JordanAceto/it_is_the_champion/faceplate/docs/2D/it_is_the_champion_faceplate-bottom.jpg

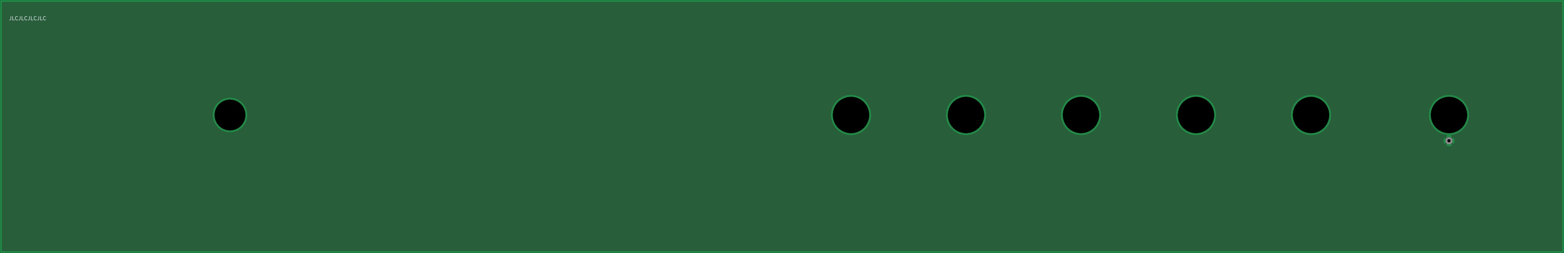
faceplate/docs/2D/it_is_the_champion_faceplate-bottom.jpg
