JordanAceto/it_is_the_champion/faceplate/docs/html_nav/images/cat_pdf_layers_it_is_the_champion_faceplate-B_Cu.png

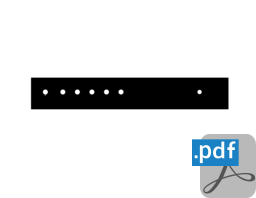
faceplate/docs/html_nav/images/cat_pdf_layers_it_is_the_champion_faceplate-B_Cu.png
