JordanAceto/it_is_the_champion/pcb/docs/2D/it_is_the_champion-bottom.jpg

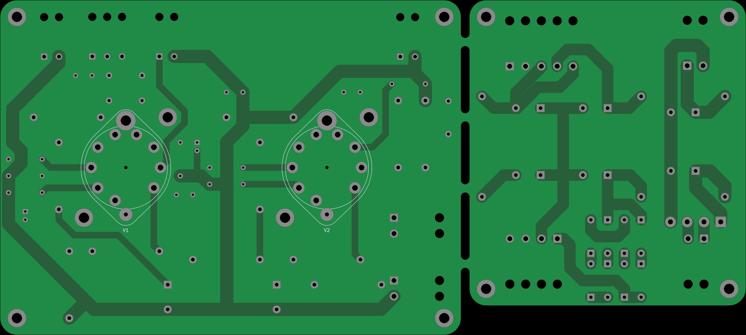
pcb/docs/2D/it_is_the_champion-bottom.jpg
