JordanAceto/it_is_the_champion/pcb/docs/html_nav/images/cat_pdf_layers_it_is_the_champion-B_Cu.png

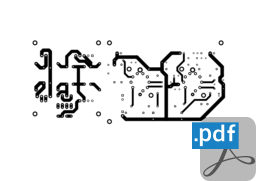
pcb/docs/html_nav/images/cat_pdf_layers_it_is_the_champion-B_Cu.png
