JordanAceto/it_is_the_champion/rear_panel/docs/2D/it_is_the_champion_rear_panel-bottom.jpg

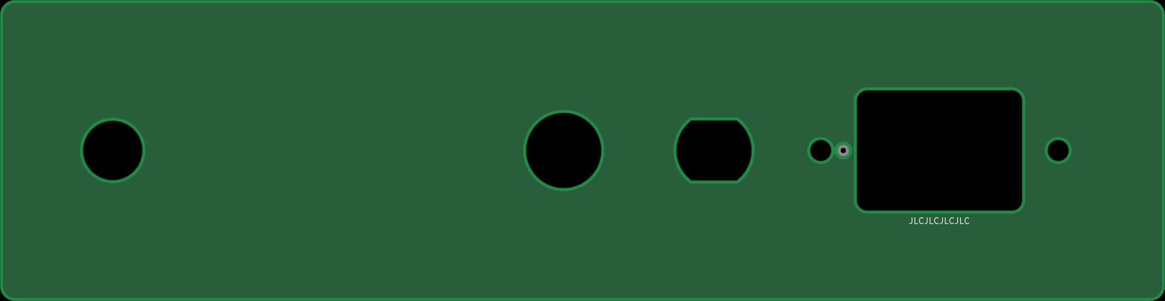
rear_panel/docs/2D/it_is_the_champion_rear_panel-bottom.jpg
