JordanAceto/it_is_the_champion/rear_panel/docs/html_nav/images/cat_pdf_layers_it_is_the_champion_rear_panel-F_Silkscreen.png

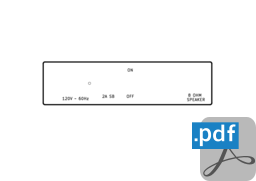
rear_panel/docs/html_nav/images/cat_pdf_layers_it_is_the_champion_rear_panel-F_Silkscreen.png
