JordanAceto/it_is_the_champion/pcb/docs/html_nav/images/cat_pdf_pcb_print_FCu_it_is_the_champion-F_Cu.png

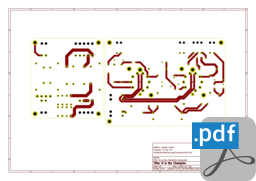
pcb/docs/html_nav/images/cat_pdf_pcb_print_FCu_it_is_the_champion-F_Cu.png
