JordanAceto/it_is_the_champion/pcb/docs/html_nav/images/cat_pdf_sch_print_it_is_the_champion-schematic.png

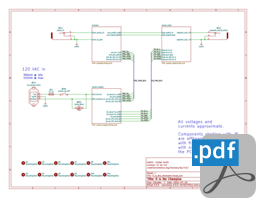
pcb/docs/html_nav/images/cat_pdf_sch_print_it_is_the_champion-schematic.png
