JordanAceto/it_is_the_champion/pcb/docs/2D/individual_layers/it_is_the_champion-F_Silkscreen.pdf

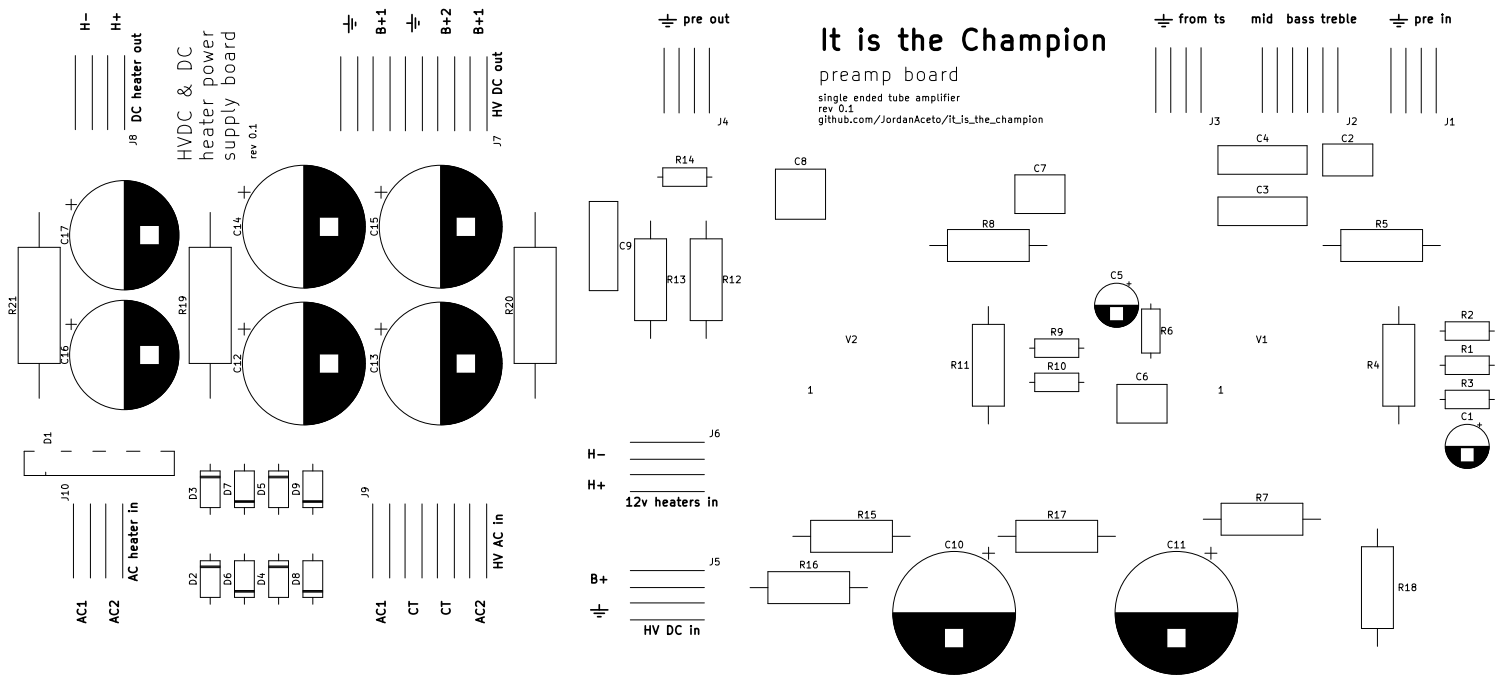
[picture p60: page 1]

It is the Champion
preamp board

single ended tube amplifier
