JordanAceto/it_is_the_champion/pcb/docs/2D/it_is_the_champion-B_Cu.pdf

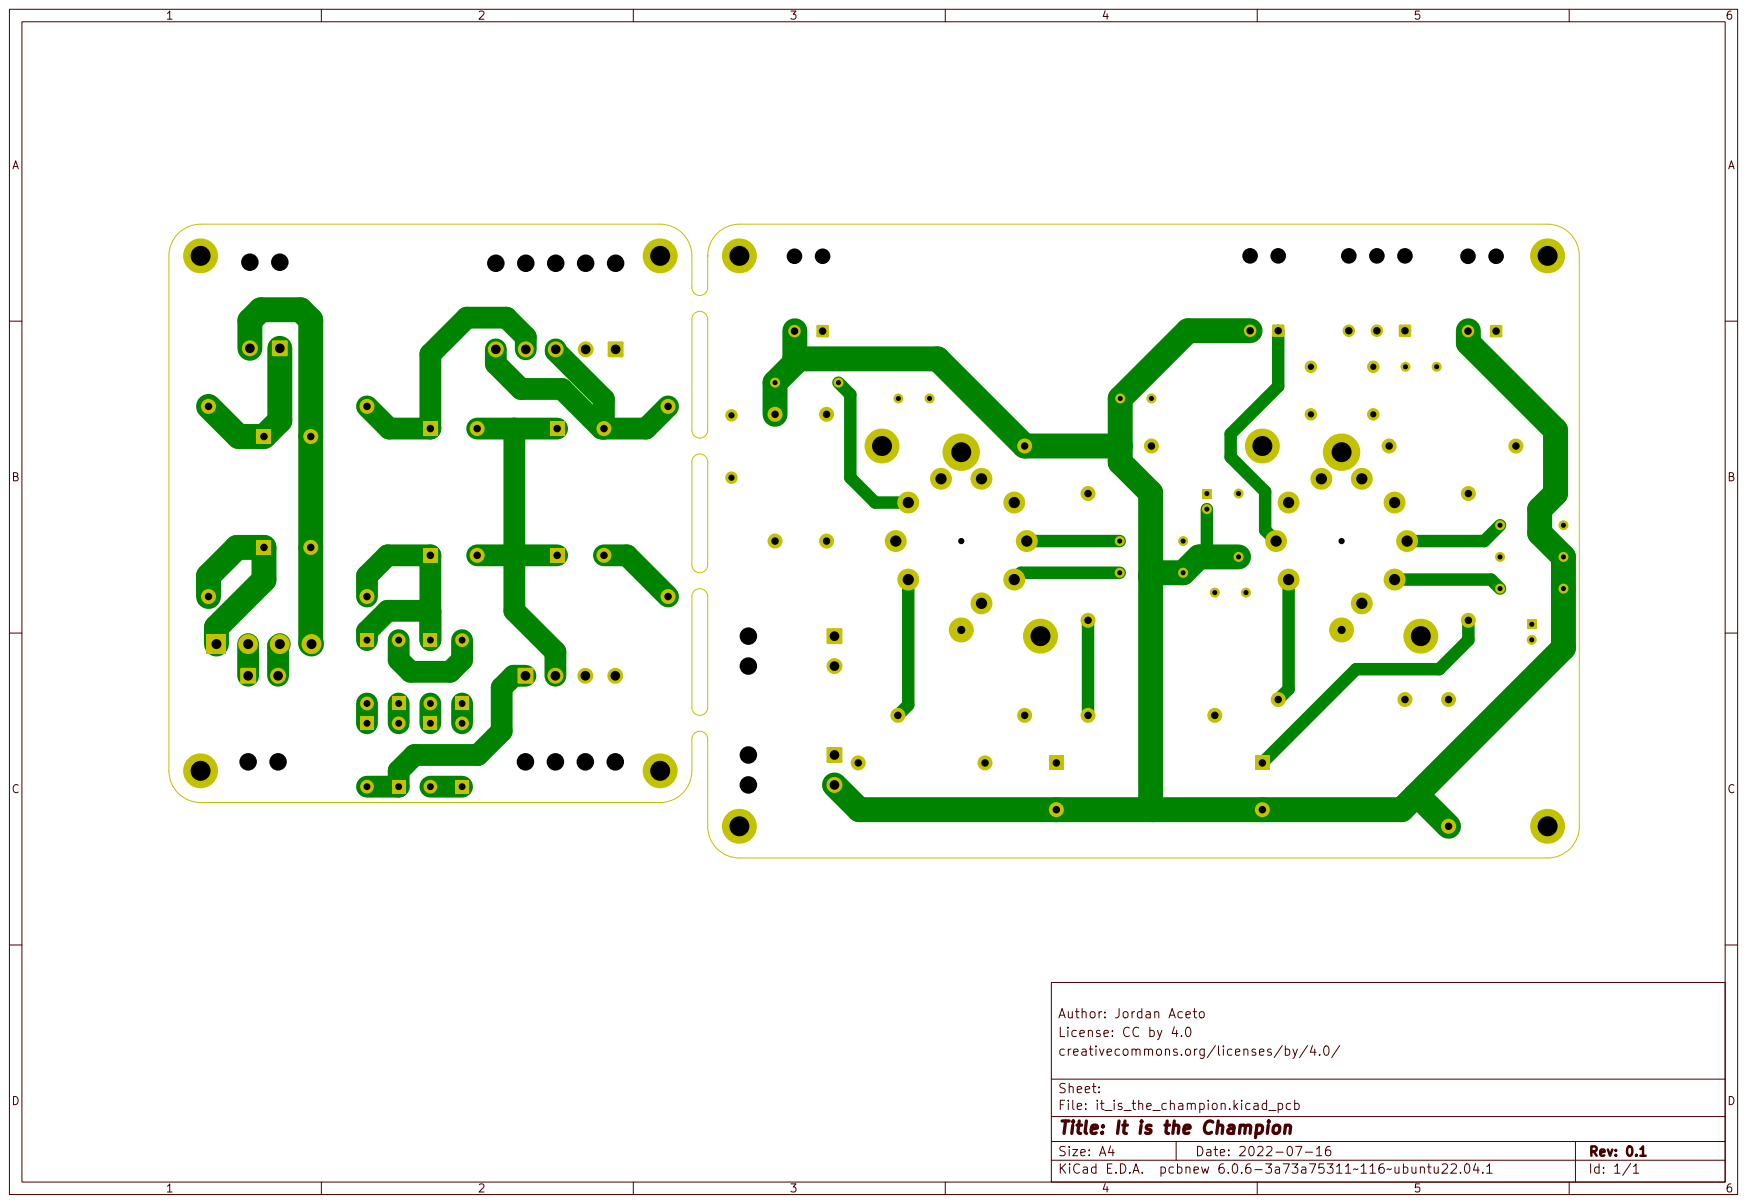
[picture p65: page 1]
