JordanAceto/it_is_the_champion/pcb/docs/2D/it_is_the_champion-F_Cu.pdf

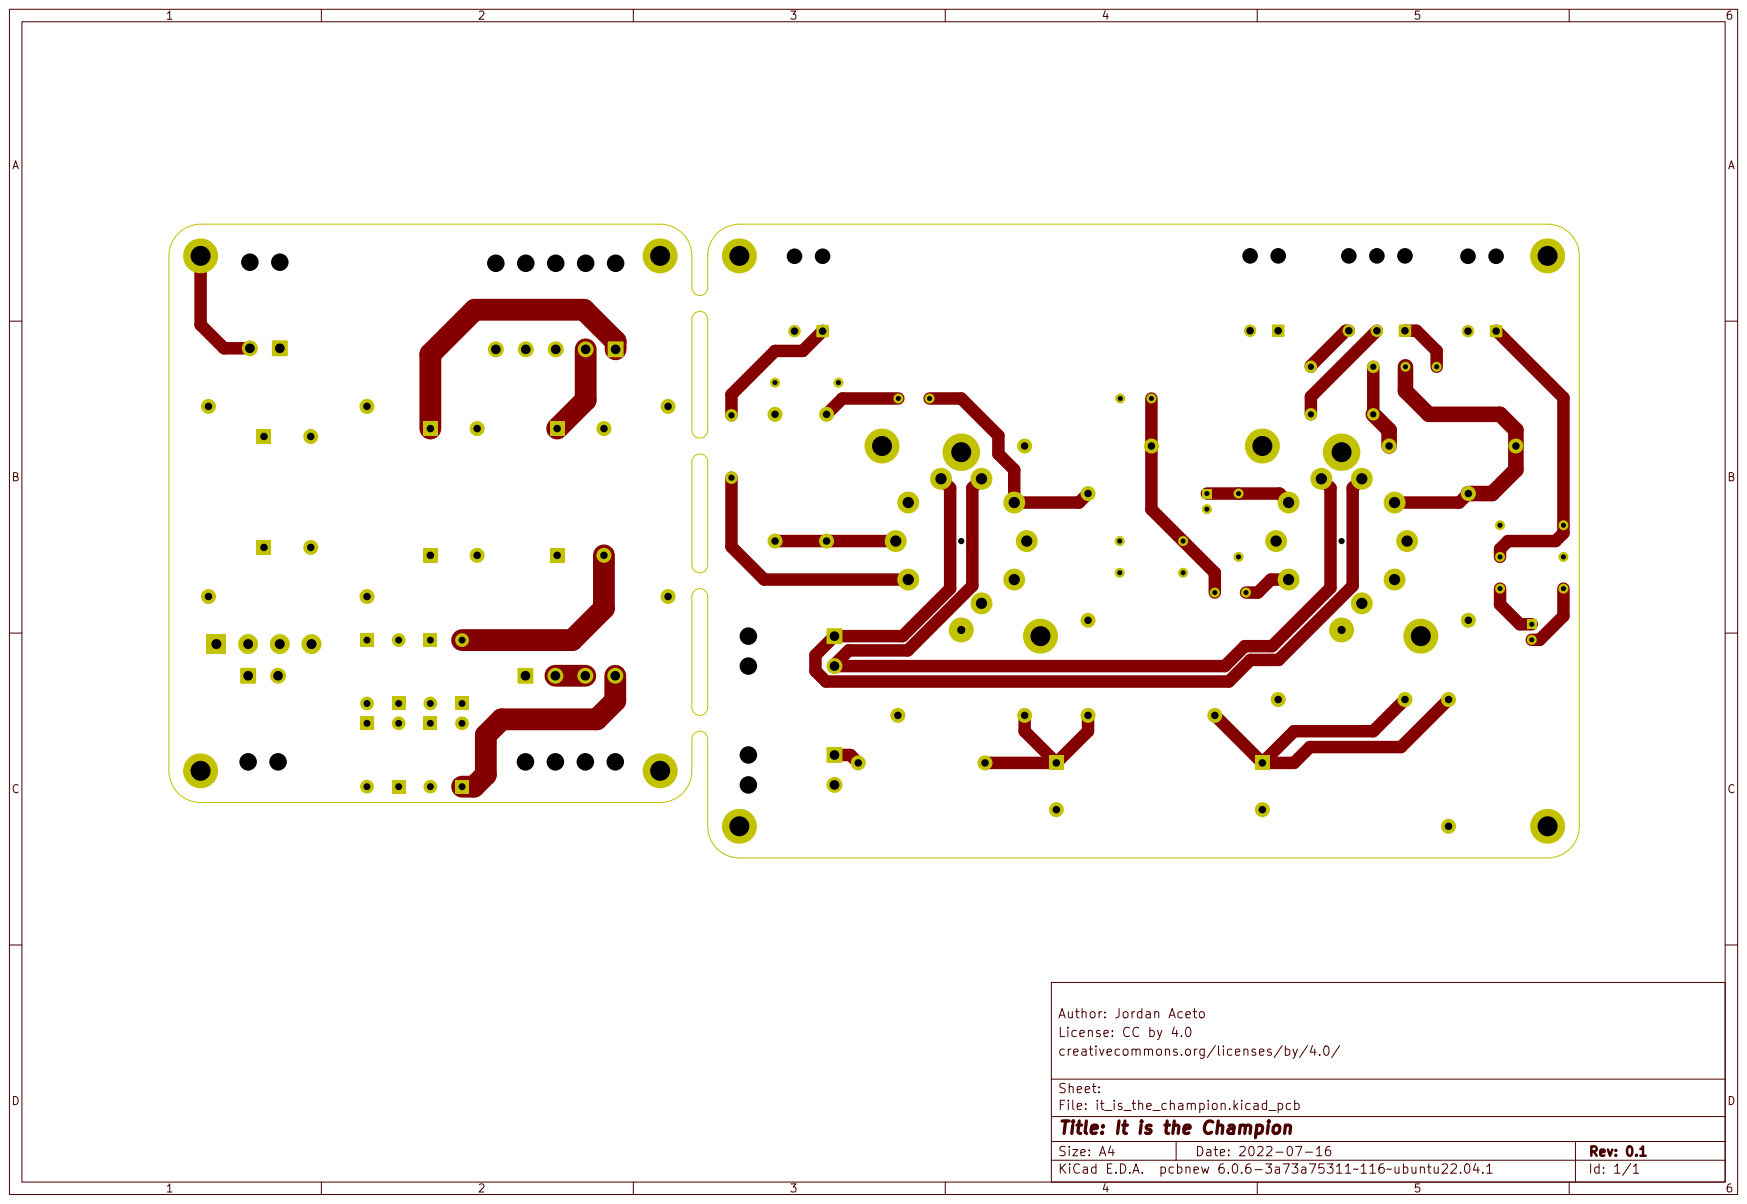
[picture p66: page 1]
