JordanAceto/it_is_the_champion/pcb/docs/2D/individual_layers/it_is_the_champion-B_Courtyard.pdf

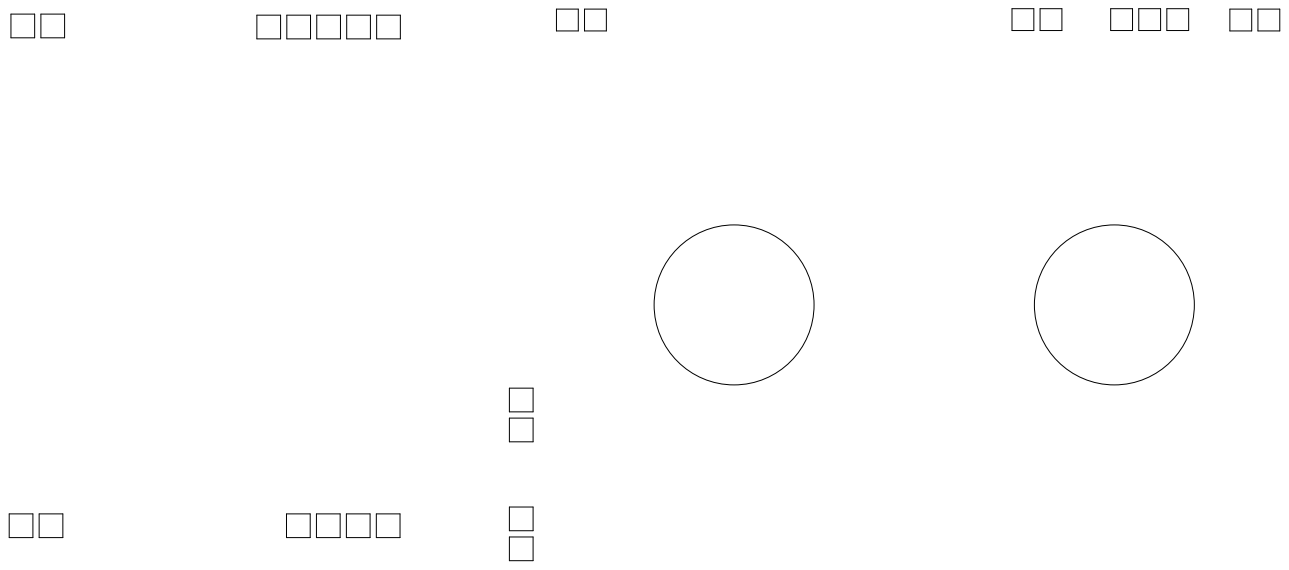
[picture p67: page 1]
