JordanAceto/it_is_the_champion/pcb/docs/2D/individual_layers/it_is_the_champion-B_Cu.pdf

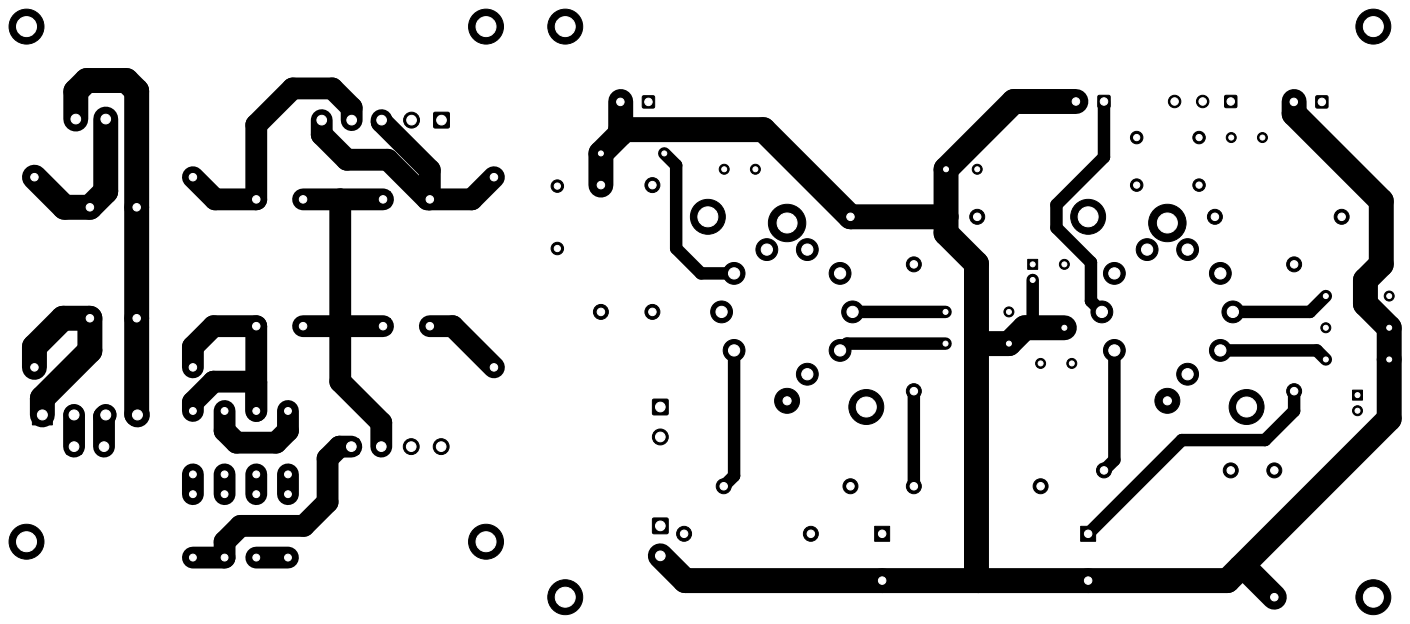
[picture p68: page 1]
