JordanAceto/it_is_the_champion/pcb/docs/2D/individual_layers/it_is_the_champion-B_Fab.pdf

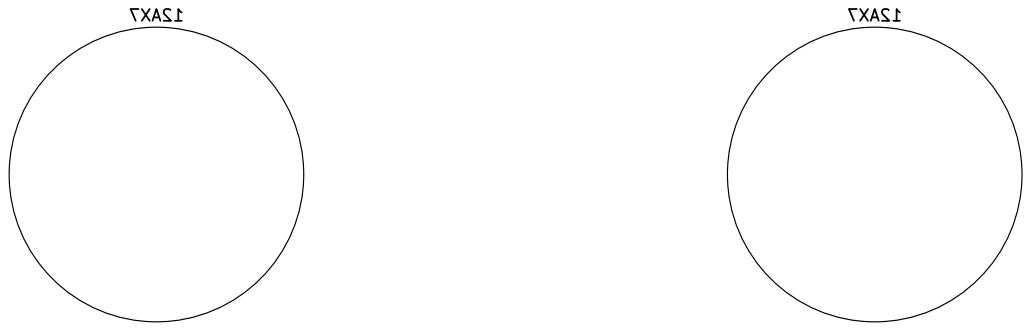
[picture p69: page 1]
