JordanAceto/it_is_the_champion/pcb/docs/2D/individual_layers/it_is_the_champion-B_Mask.pdf

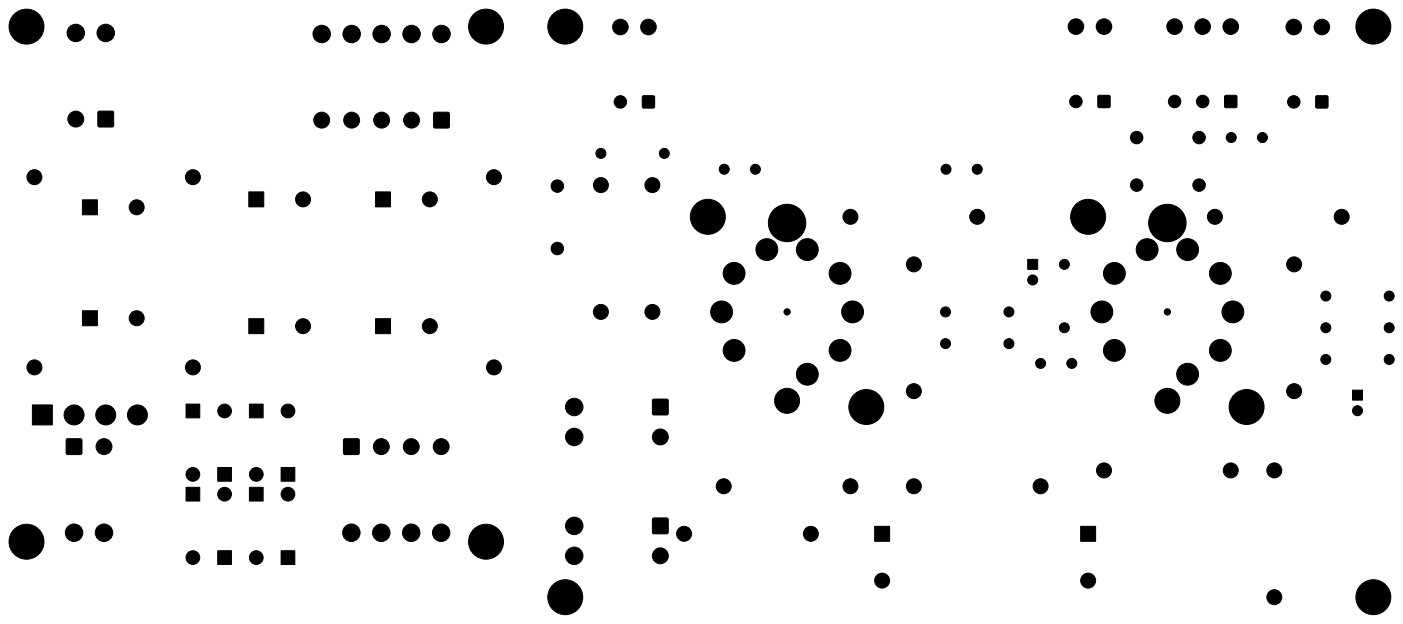
[picture p70: page 1]
