JordanAceto/it_is_the_champion/pcb/docs/2D/individual_layers/it_is_the_champion-B_Silkscreen.pdf

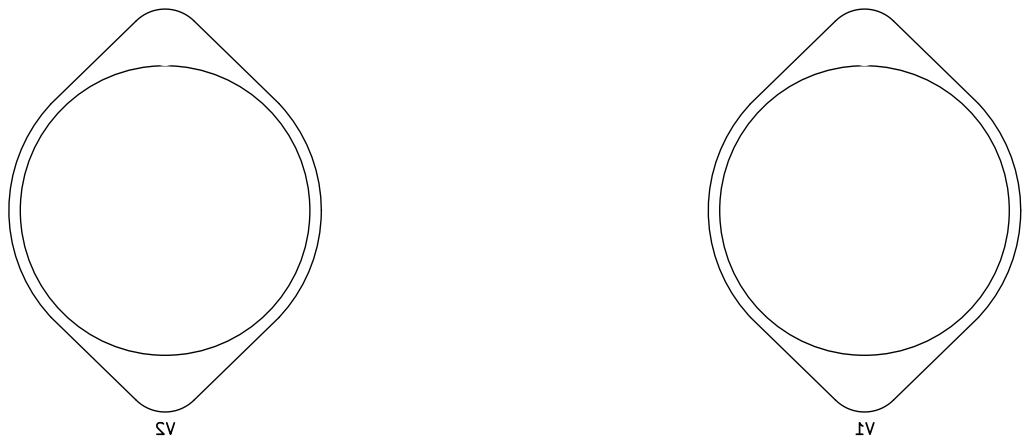
[picture p71: page 1]
