JordanAceto/it_is_the_champion/pcb/docs/2D/individual_layers/it_is_the_champion-Edge_Cuts.pdf

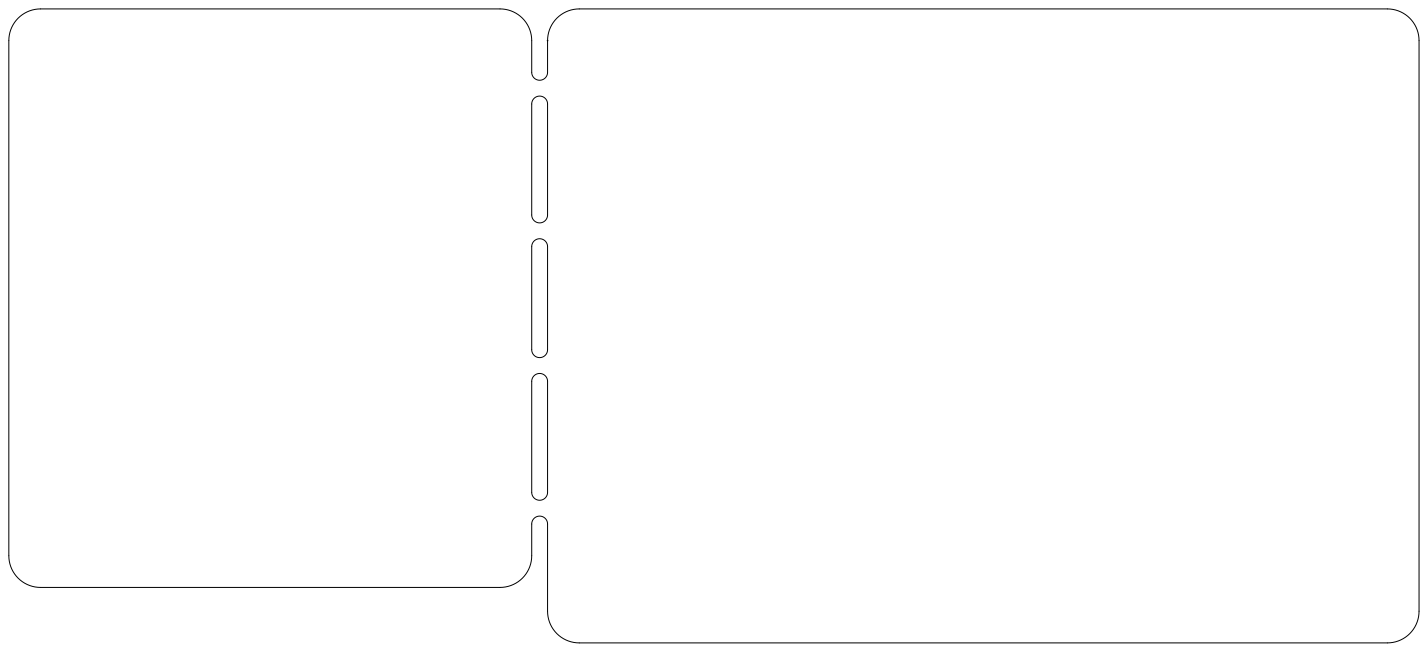
[picture p72: page 1]
