JordanAceto/it_is_the_champion/pcb/docs/2D/individual_layers/it_is_the_champion-F_Courtyard.pdf

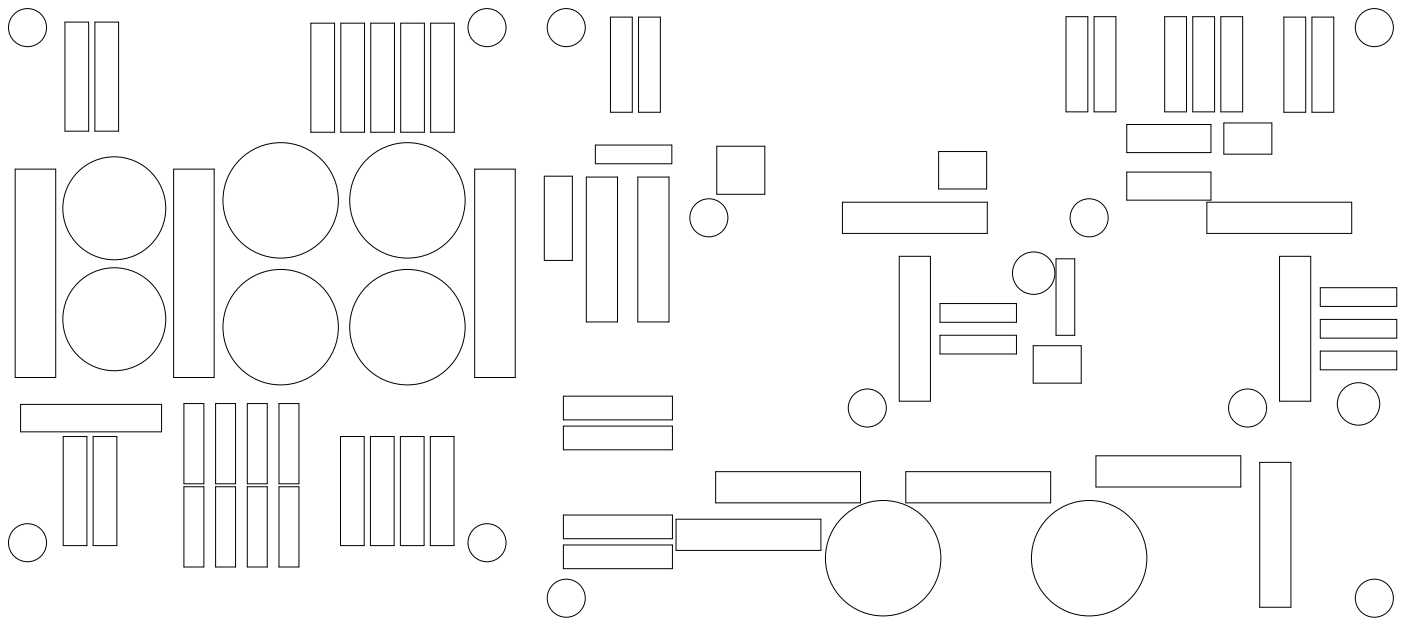
[picture p73: page 1]
