JordanAceto/it_is_the_champion/pcb/docs/2D/individual_layers/it_is_the_champion-F_Cu.pdf

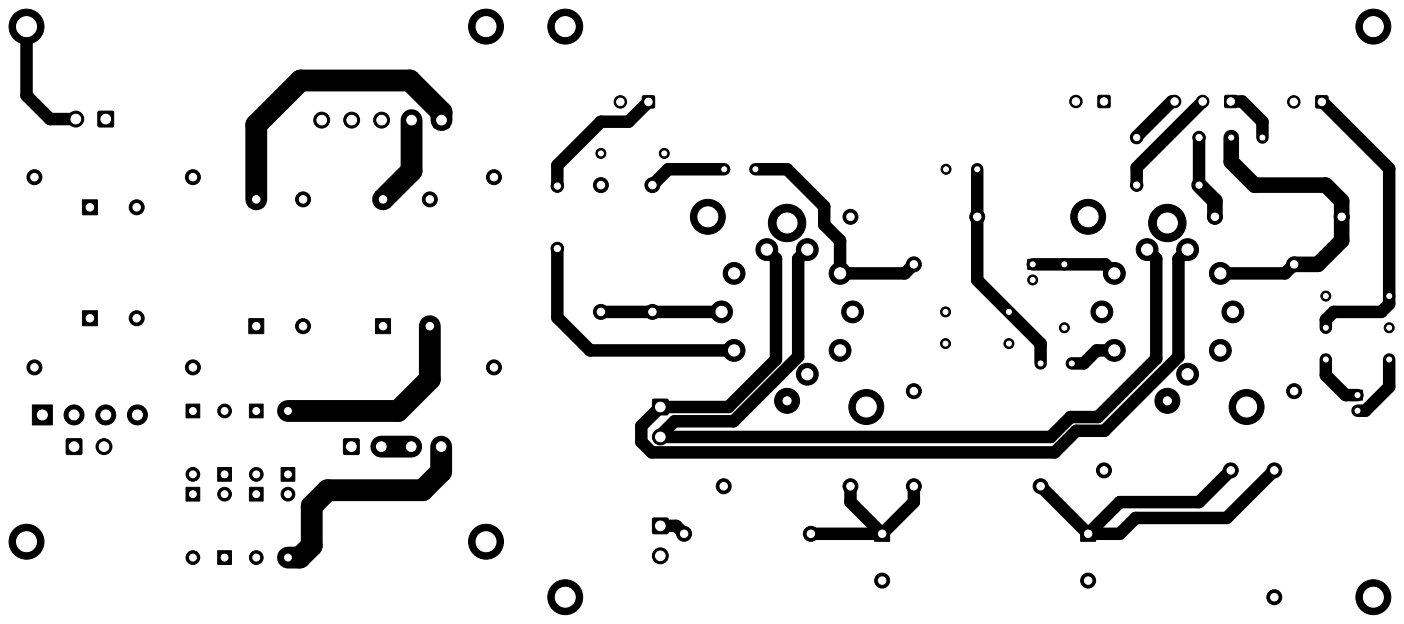
[picture p74: page 1]
