JordanAceto/it_is_the_champion/pcb/docs/2D/individual_layers/it_is_the_champion-F_Fab.pdf

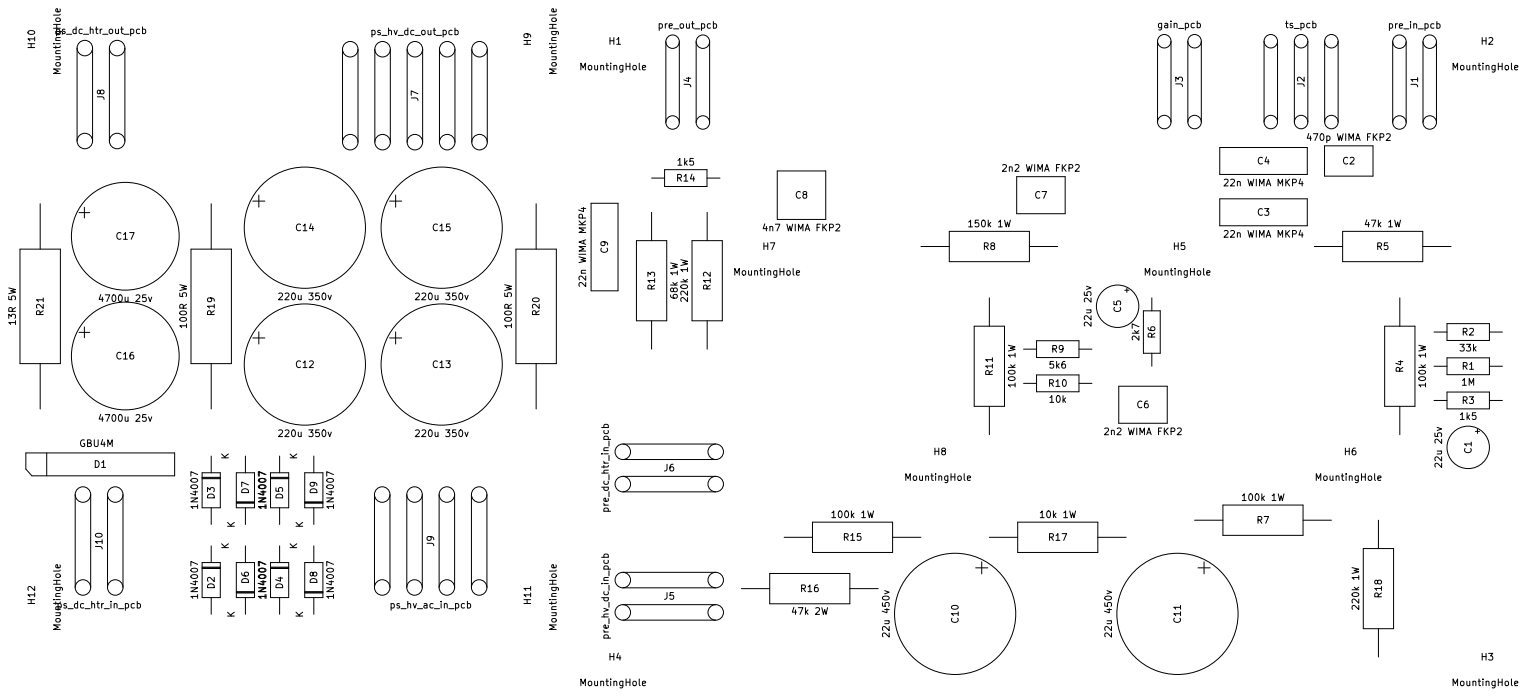
[picture p75: page 1]
