JordanAceto/it_is_the_champion/faceplate/docs/2D/individual_layers/it_is_the_champion_faceplate-B_Cu.pdf

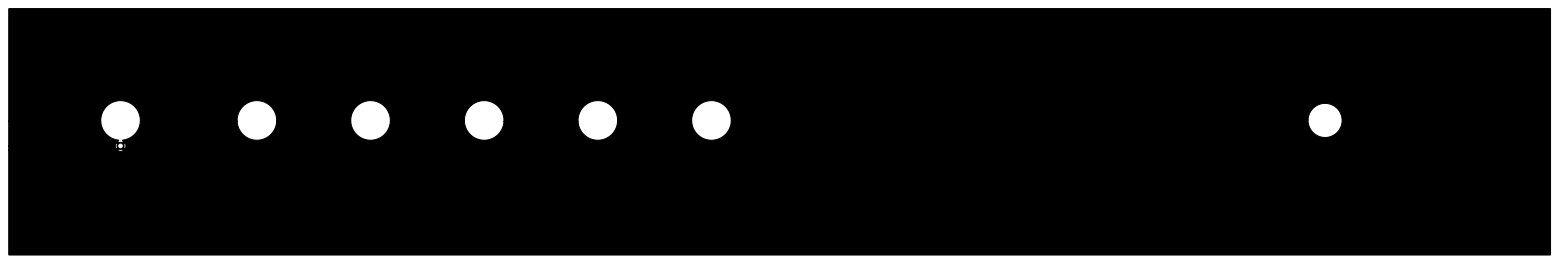
[picture p76: page 1]
