JordanAceto/it_is_the_champion/faceplate/docs/2D/individual_layers/it_is_the_champion_faceplate-Edge_Cuts.pdf

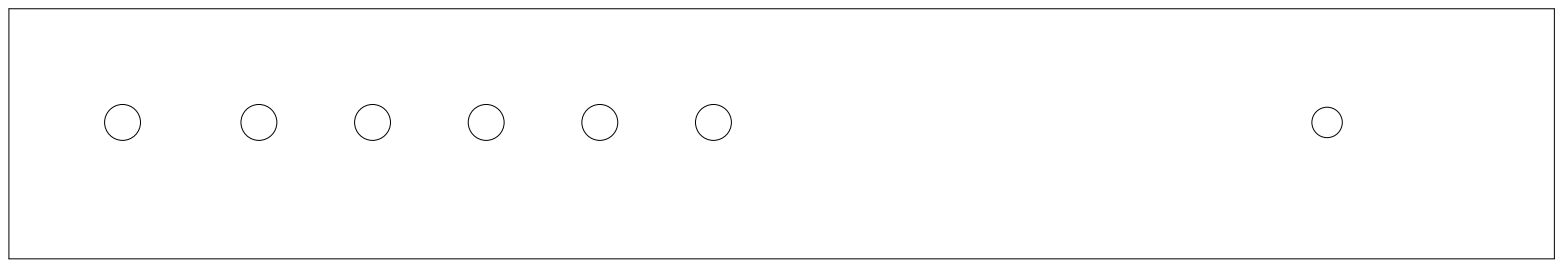
[picture p77: page 1]
