JordanAceto/it_is_the_champion/rear_panel/docs/2D/individual_layers/it_is_the_champion_rear_panel-B_Cu.pdf

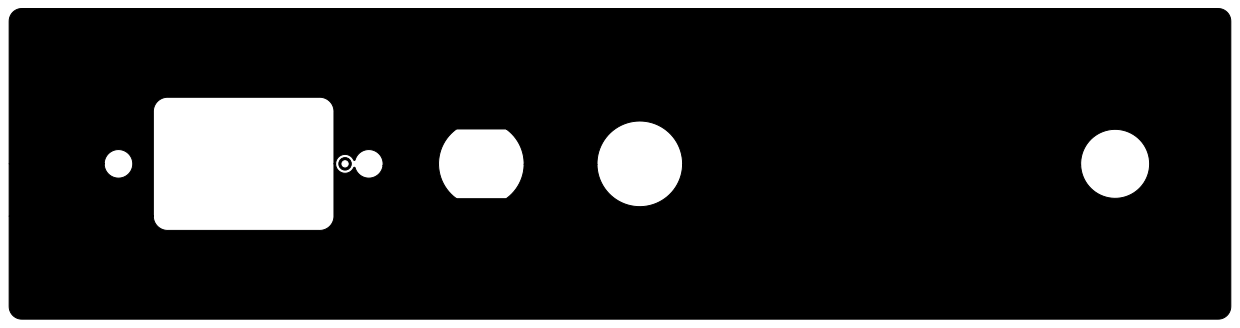
[picture p78: page 1]
