JordanAceto/it_is_the_champion/rear_panel/docs/2D/individual_layers/it_is_the_champion_rear_panel-Edge_Cuts.pdf

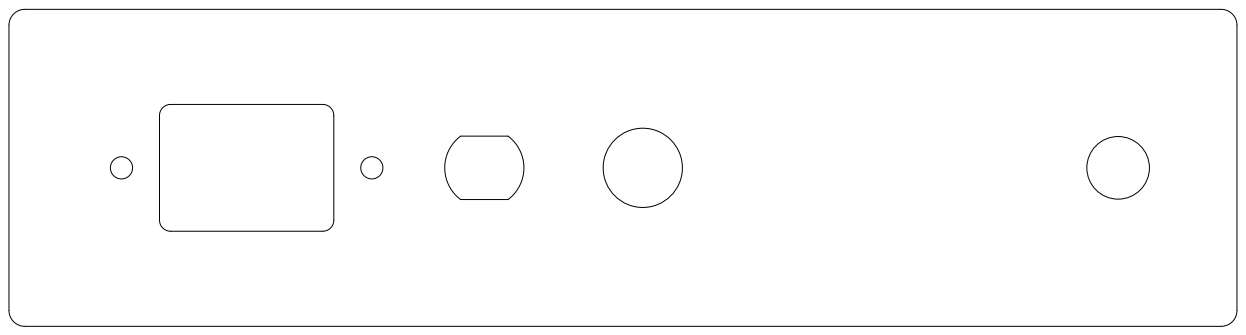
[picture p79: page 1]
