JordanAceto/it_is_the_champion/rear_panel/docs/2D/individual_layers/it_is_the_champion_rear_panel-F_Silkscreen.pdf

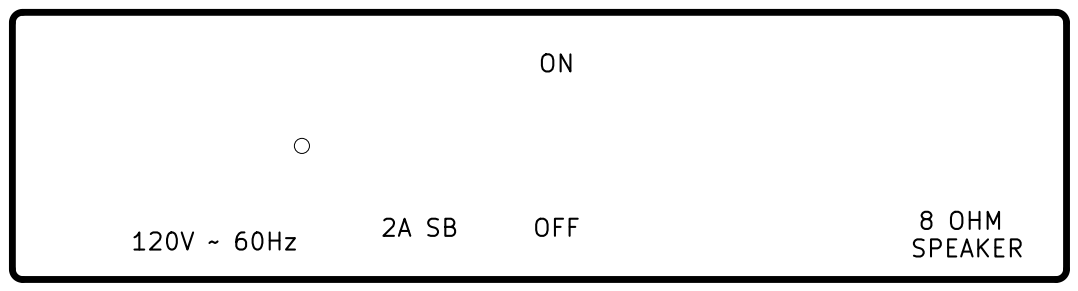
[picture p80: page 1]
