JordanAceto/it_is_the_champion/prototype/kicad_docs/power_amp.sch

## KiCad design prototype/kicad_docs/power_amp.sch (2021-08-18)

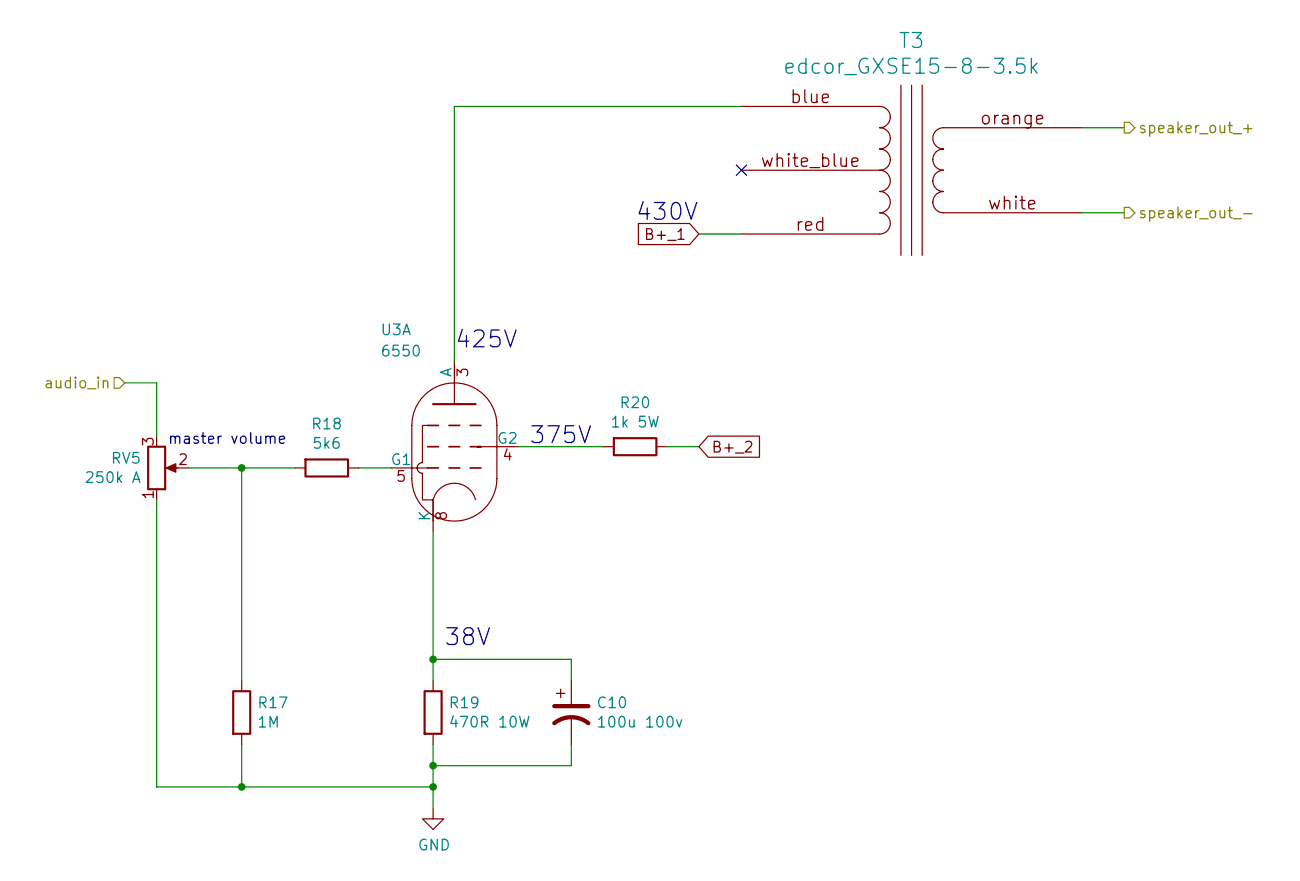
[picture p87: schematic power_amp.sch]

Parts:
C10: 100u 100v
R17: 1M
R18: 5k6
R19: 470R 10W
R20: 1k 5W
RV5: 250k A
T3: edcor_GXSE15-8-3.5k
U3: 6550; Valve_Octal

Connections:
B+_1: T3.red (16)
B+_2: R20.1
GND: C10.2, R17.2, R19.2, RV5.1
unnamed: C10.1, R19.1, U3.8 (K)
unnamed: R17.1, R18.2, RV5.2
unnamed: R18.1, U3.5 (G1)
unnamed: R20.2, U3.4 (G2)
unnamed: T3.blue, U3.3 (A)
audio_in: RV5.3
speaker_out_+: T3.orange
speaker_out_-: T3.white

Notes on the sheet:
master volume
38V
425V
375V
430V
