JordanAceto/it_is_the_champion/prototype/kicad_docs/power_supply.sch

## KiCad design prototype/kicad_docs/power_supply.sch (2021-08-18)

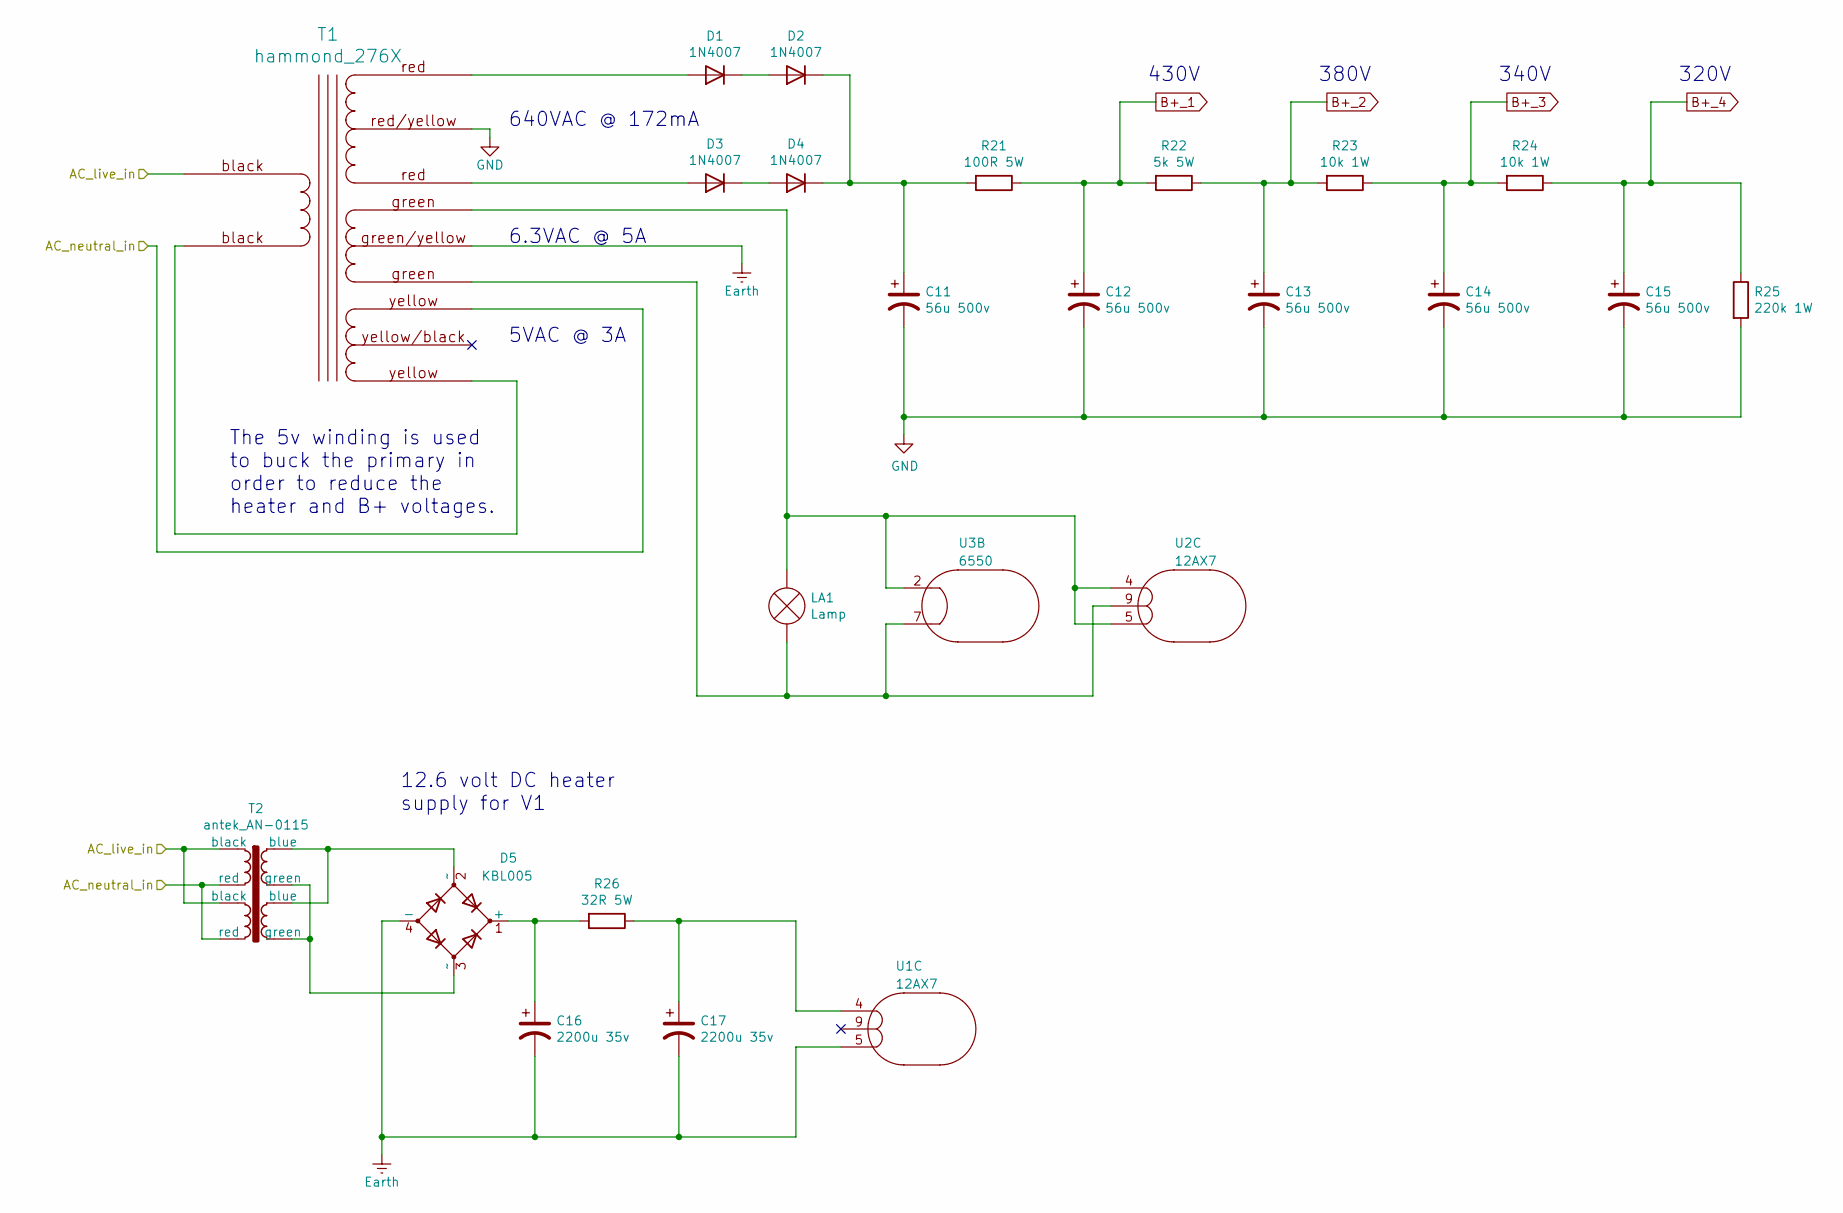
[picture p88: schematic power_supply.sch]

Parts:
C11, C12, C13, C14, C15: 56u 500v
C16, C17: 2200u 35v
D1, D2, D3, D4: 1N4007; D_DO-41_SOD81_P10.16mm_Horizontal
D5: KBL005
LA1: Lamp
R21: 100R 5W
R22: 5k 5W
R23, R24: 10k 1W
R25: 220k 1W
R26: 32R 5W
T1: hammond_276X
T2: antek_AN-0115
U1, U2: 12AX7; Valve_Noval_P
U3: 6550; Valve_Octal

Connections:
AC_live_in: T1.black, T2.1\ (black), T2.3 (black)
AC_neutral_in: T1.yellow (16), T2.2 (red), T2.4 (red)
B+_1: C12.1, R21.1, R22.2
B+_2: C13.1, R22.1, R23.2
B+_3: C14.1, R23.1, R24.2
B+_4: C15.1, R24.1, R25.1
Earth: C16.2, C17.2, D5.4 (-), T1.green/yellow, U1.5
GND: C11.2, C12.2, C13.2, C14.2, C15.2, R25.2, T1.red/yellow
unnamed: C11.1, D2.1 (K), D4.1 (K), R21.2
unnamed: C16.1, D5.1 (+), R26.2
unnamed: C17.1, R26.1, U1.4
unnamed: D1.1 (K), D2.2 (A)
unnamed: D1.2 (A), T1.red (16)
unnamed: D3.1 (K), D4.2 (A)
unnamed: D3.2 (A), T1.red (16)
unnamed: D5.2 (~~), T2.6 (blue), T2.8 (blue)
unnamed: D5.3 (~~), T2.5 (green), T2.7 (green)
unnamed: LA1.1 (-), T1.green, U2.9, U3.7
unnamed: LA1.2 (+), T1.green, U2.4, U2.5, U3.2
unnamed: T1.black, T1.yellow (16)

Notes on the sheet:
640VAC @ 172mA
5VAC @ 3A
6.3VAC @ 5A
The 5v winding is used to buck the primary in order to reduce the heater and B+ voltages.
430V
380V
340V
320V
12.6 volt DC heater supply for V1
