JordanAceto/it_is_the_champion/prototype/kicad_docs/preamp.sch

## KiCad design prototype/kicad_docs/preamp.sch (2021-08-25)

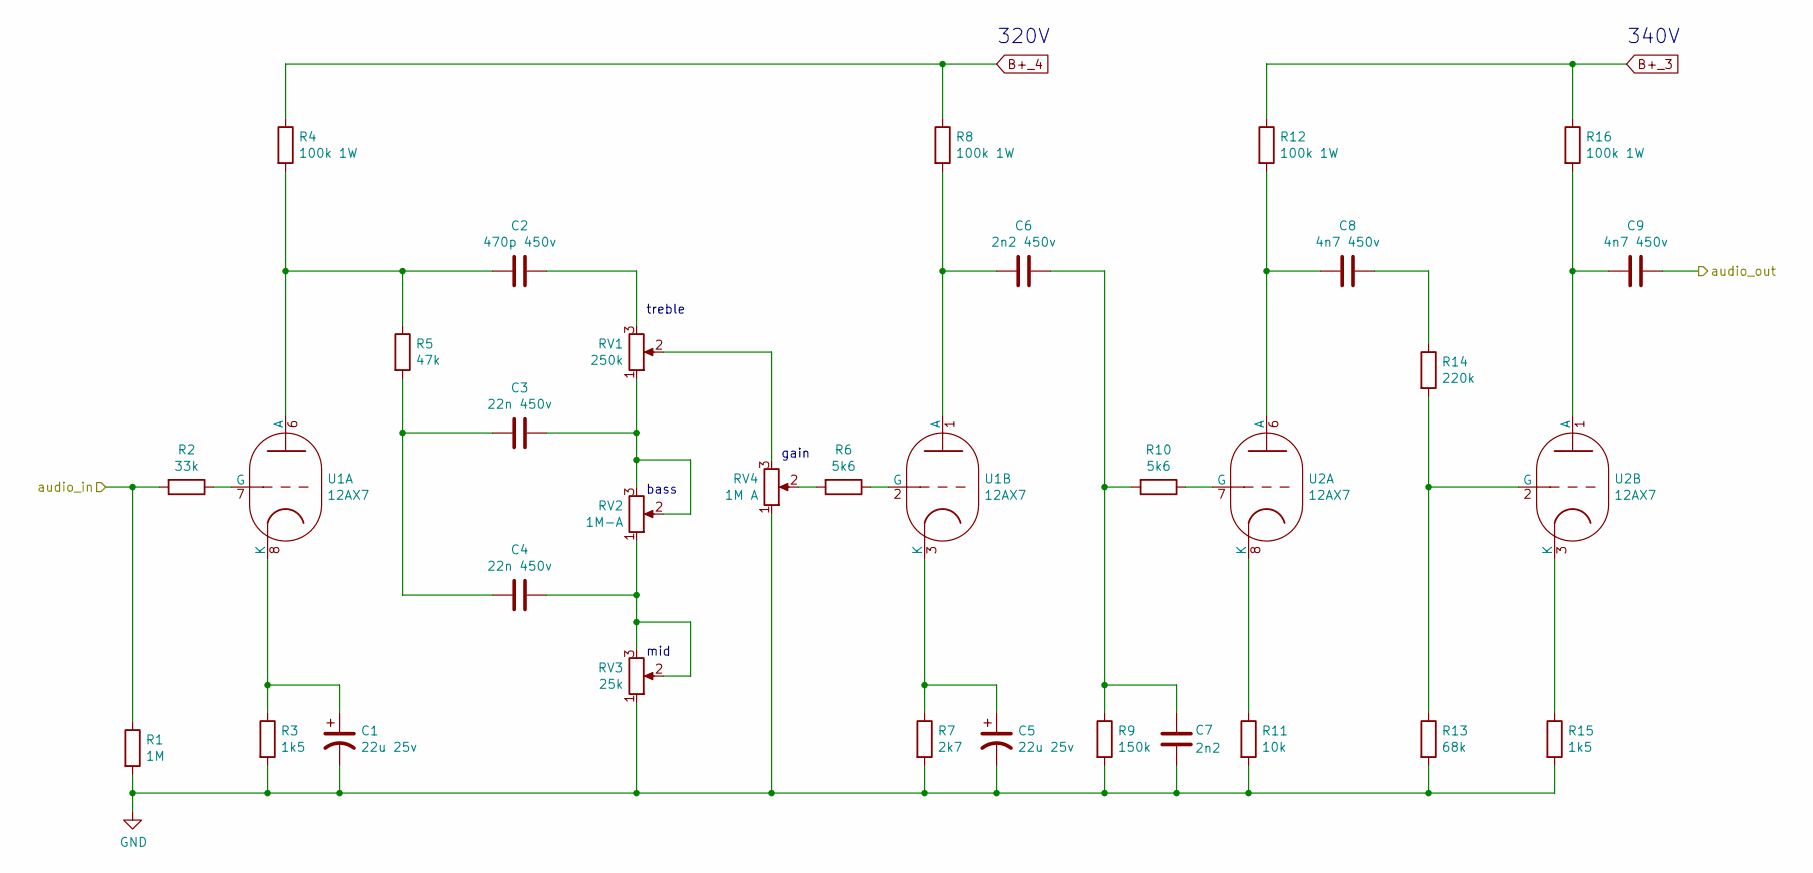
[picture p89: schematic preamp.sch]

Parts:
C1, C5: 22u 25v
C2: 470p 450v
C3, C4: 22n 450v
C6: 2n2 450v
C7: 2n2
C8, C9: 4n7 450v
R1: 1M
R2: 33k
R3, R15: 1k5
R4, R8, R12, R16: 100k 1W
R5: 47k
R6, R10: 5k6
R7: 2k7
R9: 150k
R11: 10k
R13: 68k
R14: 220k
RV1: 250k
RV2: 1M-A
RV3: 25k
RV4: 1M A
U1, U2: 12AX7; Valve_Noval_P

Connections:
B+_3: R12.1, R16.1
B+_4: R4.1, R8.1
GND: C1.2, C5.2, C7.2, R1.2, R3.2, R7.2, R9.2, R11.2, R13.2, R15.2, RV3.1, RV4.1
unnamed: C1.1, R3.1, U1.8 (K)
unnamed: C2.1, RV1.3
unnamed: C2.2, R4.2, R5.1, U1.6 (A)
unnamed: C3.1, RV1.1, RV2.2, RV2.3
unnamed: C3.2, C4.2, R5.2
unnamed: C4.1, RV2.1, RV3.2, RV3.3
unnamed: C5.1, R7.1, U1.3 (K)
unnamed: C6.1, C7.1, R9.1, R10.2
unnamed: C6.2, R8.2, U1.1 (A)
unnamed: C8.1, R14.1
unnamed: C8.2, R12.2, U2.6 (A)
unnamed: C9.2, R16.2, U2.1 (A)
unnamed: R2.1, U1.7 (G)
unnamed: R6.1, U1.2 (G)
unnamed: R6.2, RV4.2
unnamed: R10.1, U2.7 (G)
unnamed: R11.1, U2.8 (K)
unnamed: R13.1, R14.2, U2.2 (G)
unnamed: R15.1, U2.3 (K)
unnamed: RV1.2, RV4.3
audio_in: R1.1, R2.2
audio_out: C9.1

Notes on the sheet:
gain
treble
bass
mid
340V
320V
