JordanAceto/it_is_the_champion/prototype/kicad_docs/single_ended_tube_amp.sch

## KiCad design prototype/kicad_docs/single_ended_tube_amp.sch (2021-08-18)

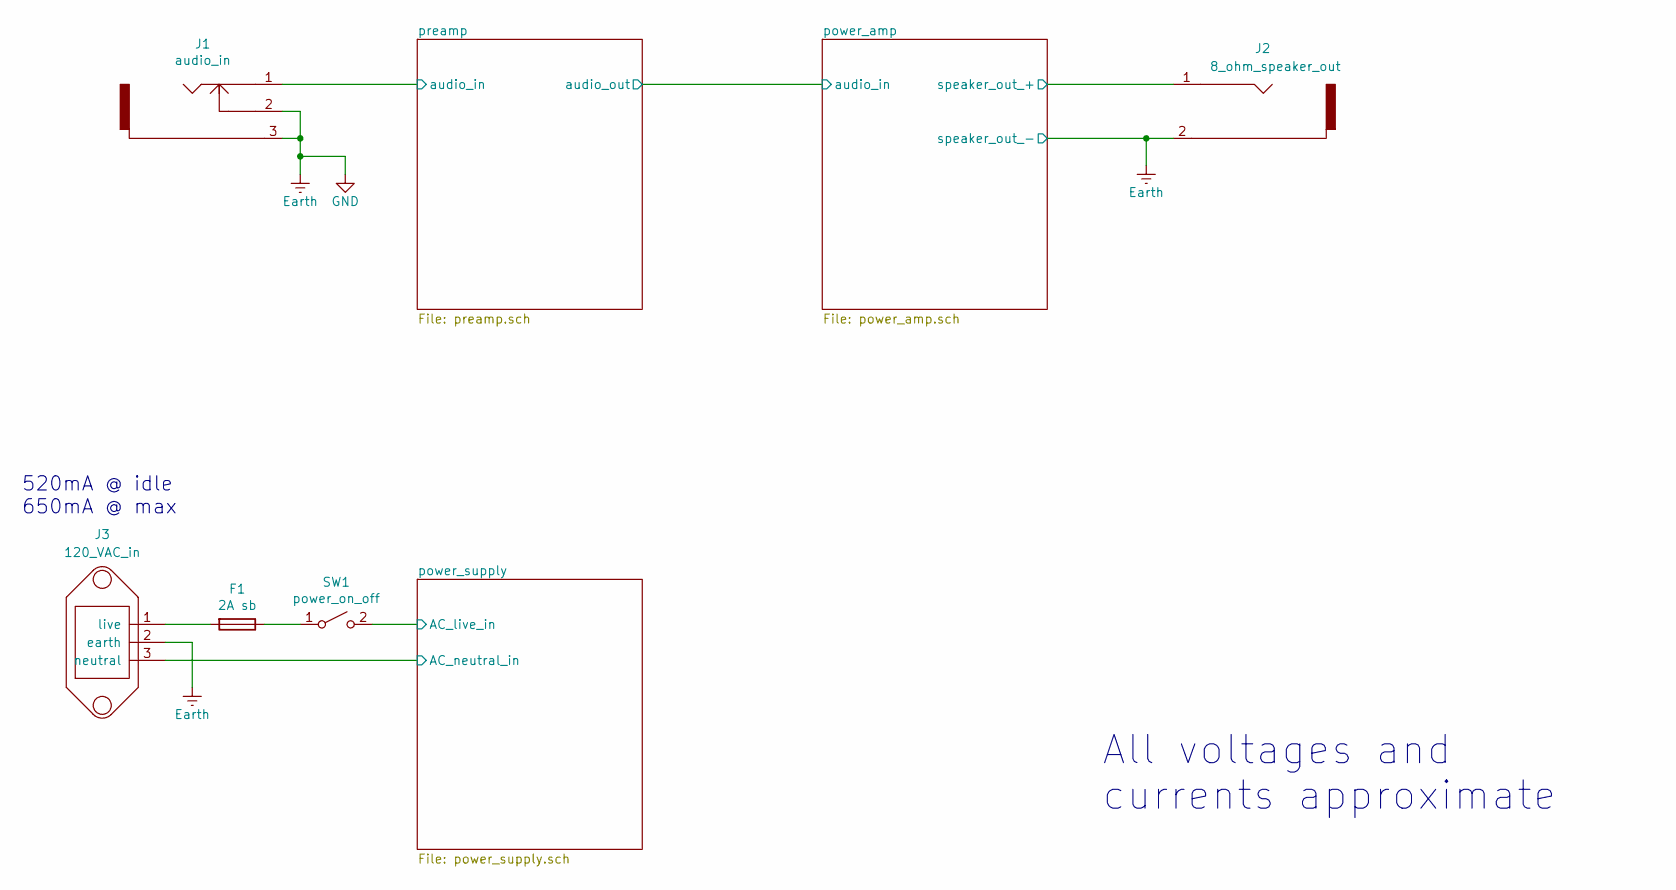
[picture p90: schematic single_ended_tube_amp.sch]

Parts:
F1: 2A sb
J1: audio_in
J2: 8_ohm_speaker_out
J3: 120_VAC_in
SW1: power_on_off

Connections:
AC_live_in: SW1.2 (B)
AC_neutral_in: J3.3 (neutral)
Earth: J1.2, J1.3, J2.2, J3.2 (earth)
unnamed: F1.1, SW1.1 (A)
unnamed: F1.2, J3.1 (live)
audio_in: J1.1
speaker_out_+: J2.1

Notes on the sheet:
520mA @ idle 650mA @ max
All voltages and currents approximate
